Armchair-Heavy-Industries/P-REXZ/DXF+Drawings/ElectronicsPlates/UpperElectronicsPlate.dxf

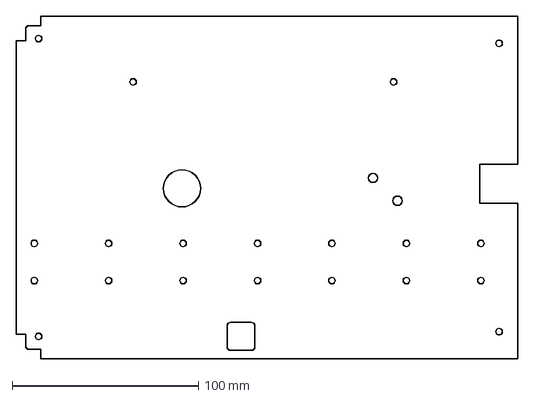
[picture p18: CAD file, 2024-03-05]
DXF+Drawings/ElectronicsPlates/UpperElectronicsPlate.dxf
269.5 x 184.0 mm
