Armchair-Heavy-Industries/P-REXZ/STLs/Toolhead/Dragonfly BMO/V1 - Klicky Mount.stl

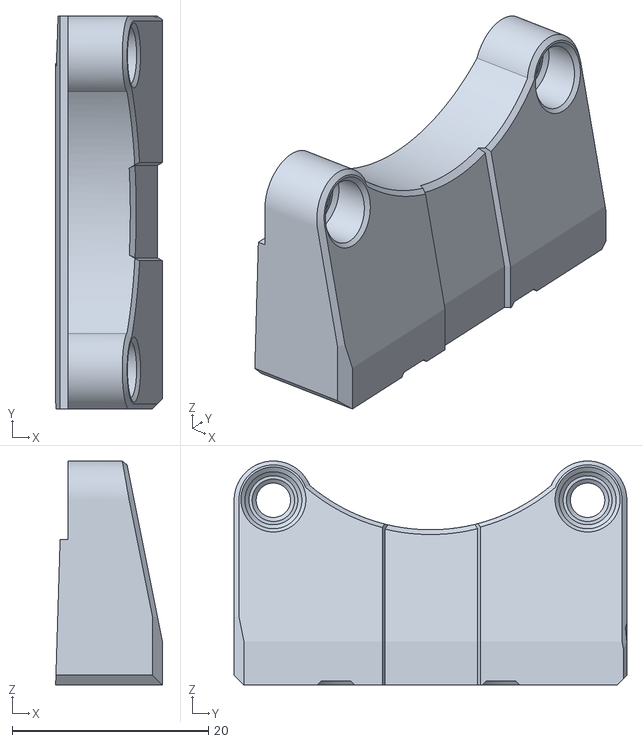
[picture p19: CAD file, 2022-03-19]
STLs/Toolhead/Dragonfly BMO/V1 - Klicky Mount.stl
10.9 x 40.0 x 22.8
