Armchair-Heavy-Industries/P-REXZ/STLs/Toolhead/Revo/V1 - Air Guide-Face - 3010.stl

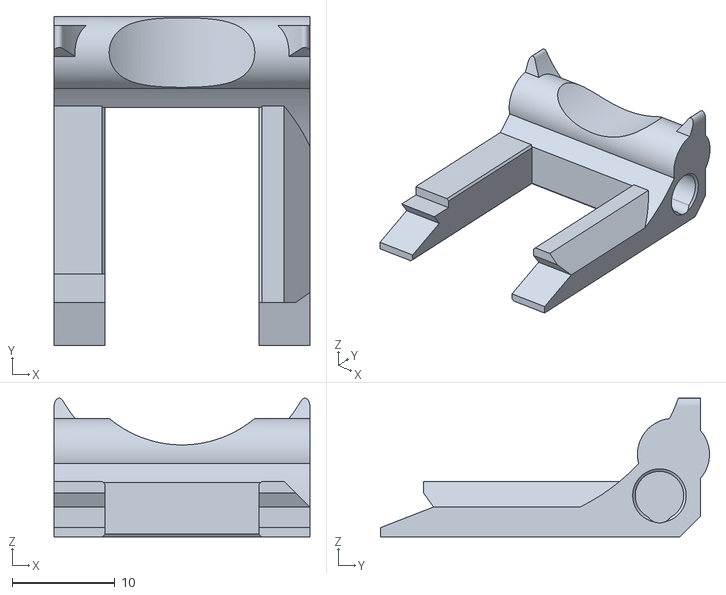
[picture p20: CAD file, 2022-03-19]
STLs/Toolhead/Revo/V1 - Air Guide-Face - 3010.stl
24.8 x 31.9 x 13.5
