Armchair-Heavy-Industries/P-REXZ/STLs/Toolhead/Dragonfly BMO/V1 - 4007 Grill.stl

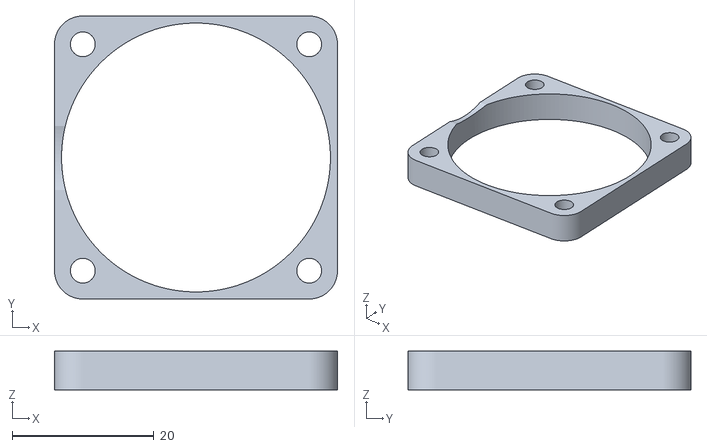
[picture p21: CAD file, 2022-03-19]
STLs/Toolhead/Dragonfly BMO/V1 - 4007 Grill.stl
40.0 x 40.0 x 5.50
