Armchair-Heavy-Industries/P-REXZ/STLs/Toolhead/Rapido/V1 - 4007 Fan - 3mm Spacer.stl

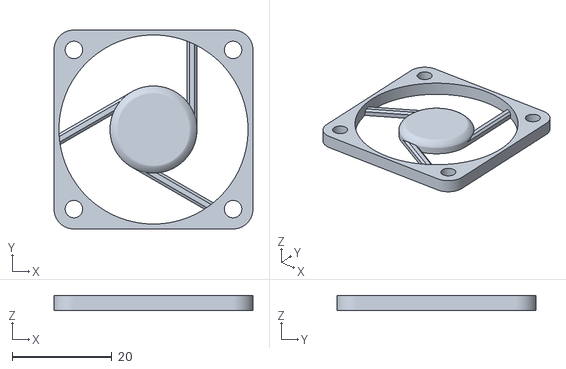
[picture p22: CAD file, 2022-03-19]
STLs/Toolhead/Rapido/V1 - 4007 Fan - 3mm Spacer.stl
40.0 x 40.0 x 3.00
