Armchair-Heavy-Industries/P-REXZ/STLs/Toolhead/Revo/V1 - Revo Micro - Hotend Mount.stl

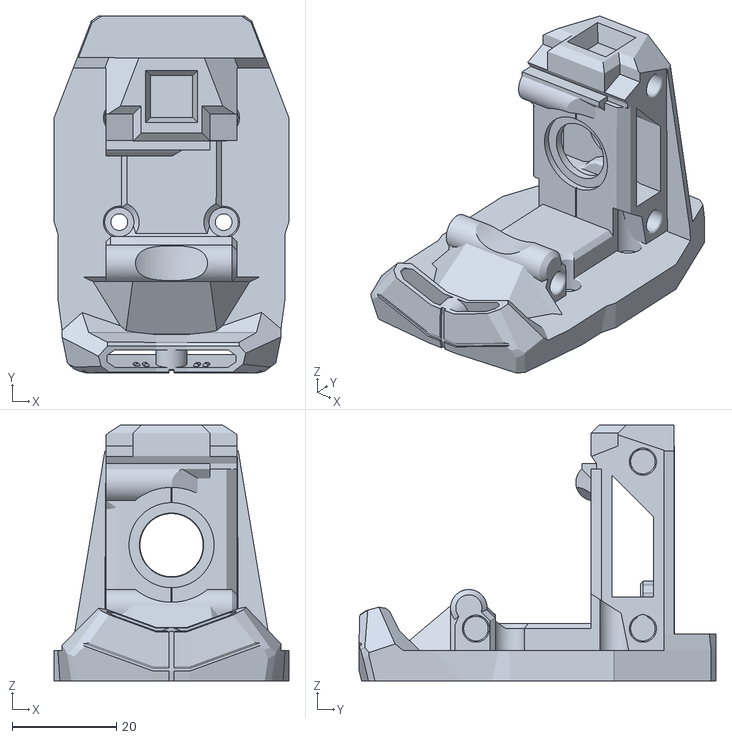
[picture p23: CAD file, 2022-03-19]
STLs/Toolhead/Revo/V1 - Revo Micro - Hotend Mount.stl
45.0 x 68.4 x 49.0
