Armchair-Heavy-Industries/P-REXZ/STLs/Toolhead/Dragonfly BMO/[a]_V1 - 3010 Speed Fairing.stl

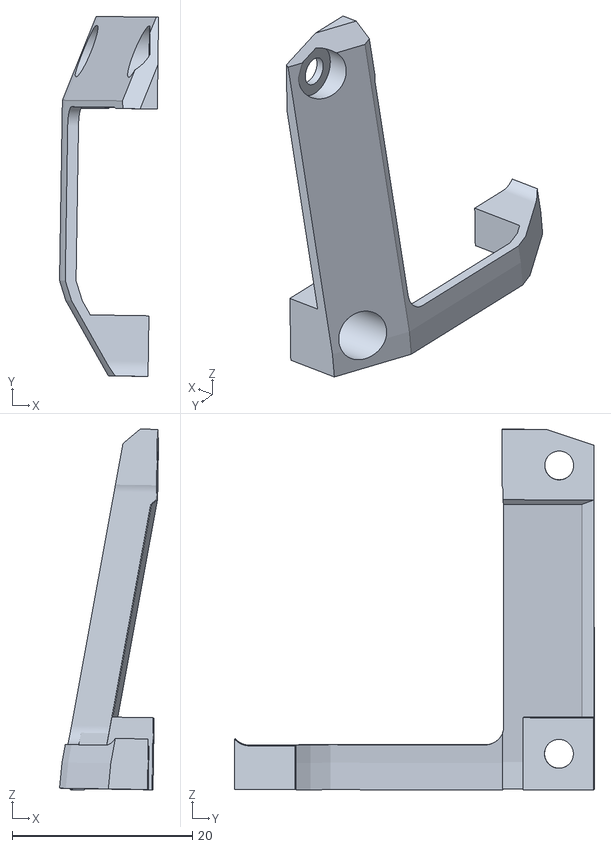
[picture p24: CAD file, 2022-03-19]
STLs/Toolhead/Dragonfly BMO/[a]_V1 - 3010 Speed Fairing.stl
11.0 x 39.9 x 40.0
