Armchair-Heavy-Industries/P-REXZ/STLs/Toolhead/Rapido/V1 - Rapido - Hotend Mount - V1.stl

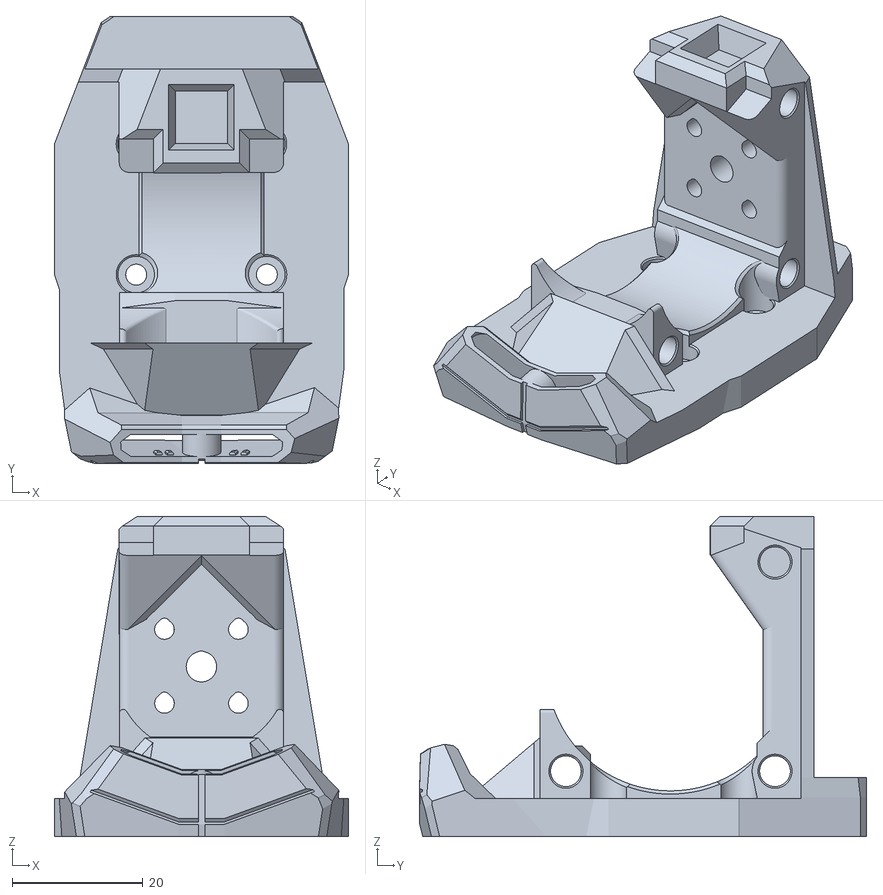
[picture p25: CAD file, 2022-03-19]
STLs/Toolhead/Rapido/V1 - Rapido - Hotend Mount - V1.stl
45.0 x 68.4 x 49.0
