Armchair-Heavy-Industries/P-REXZ/STLs/Toolhead/Dragonfly BMO/[a]_V1 - DD Mount Cap.stl

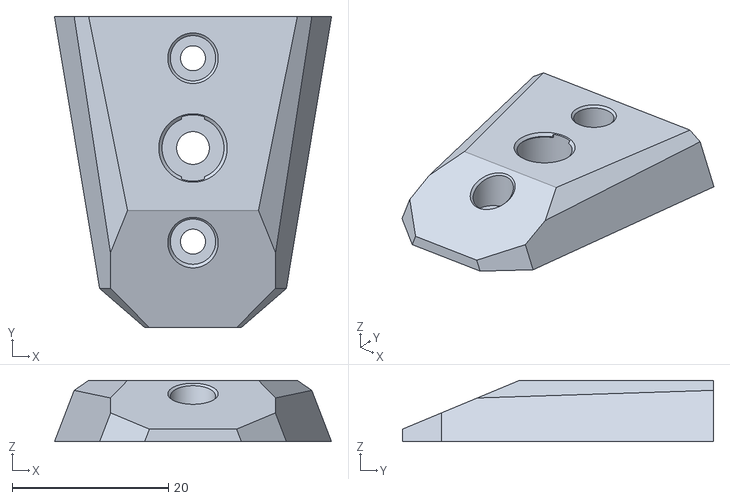
[picture p26: CAD file, 2022-03-19]
STLs/Toolhead/Dragonfly BMO/[a]_V1 - DD Mount Cap.stl
35.5 x 39.9 x 7.85
