Armchair-Heavy-Industries/P-REXZ/STLs/Toolhead/Rapido/[a]_Rapido - V1 - Air Guide-Face.stl

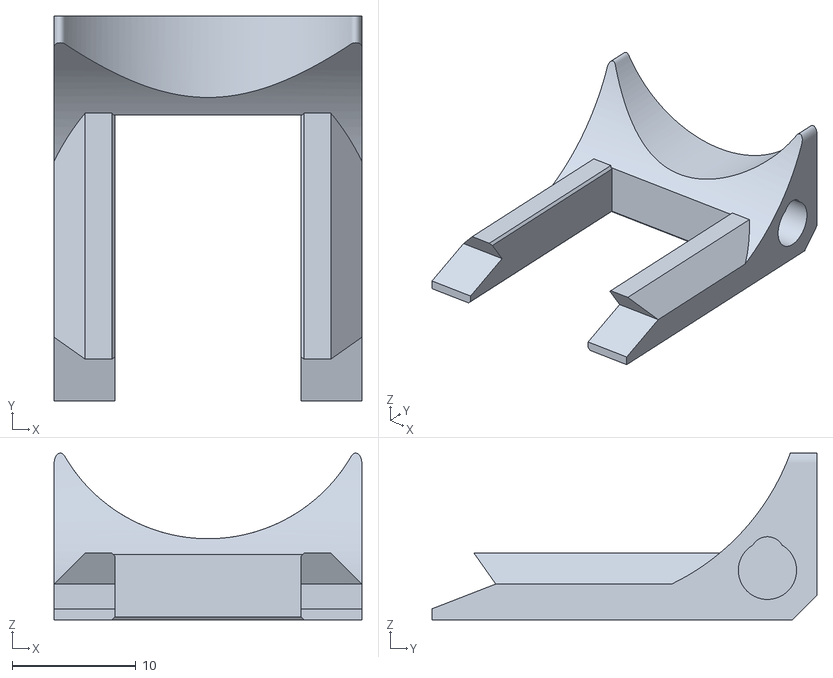
[picture p27: CAD file, 2022-03-19]
STLs/Toolhead/Rapido/[a]_Rapido - V1 - Air Guide-Face.stl
24.9 x 31.1 x 13.5
